MATTMCCA/Heliotrope/Case/OSHCut/036.jpeg

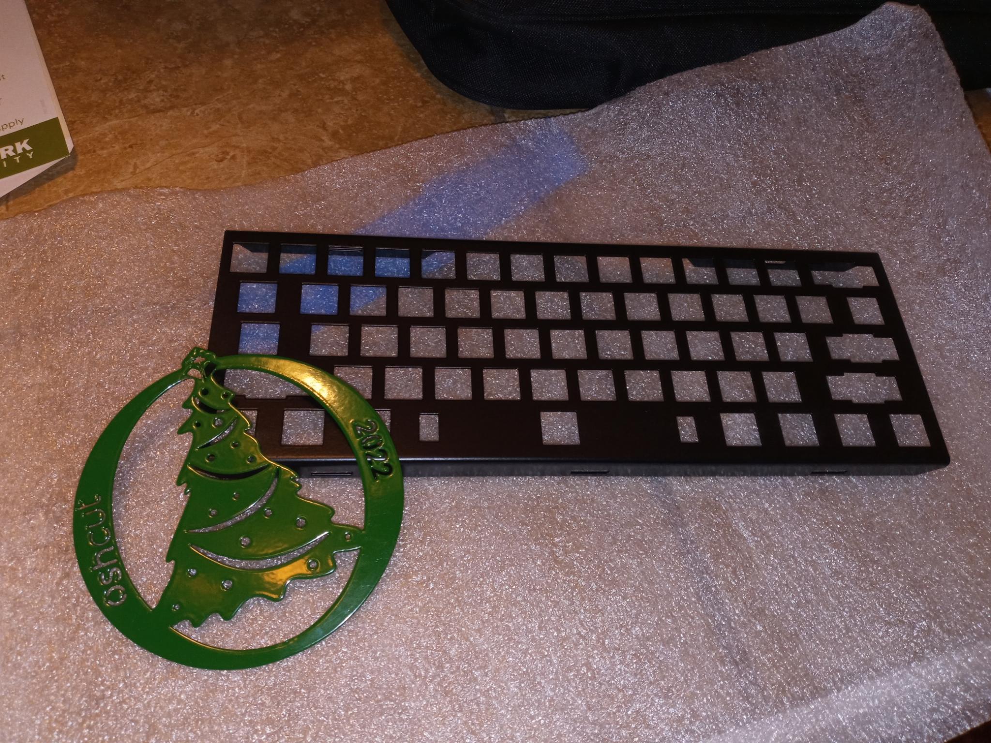
Case/OSHCut/036.jpeg
