MATTMCCA/Heliotrope/Case/ProtoTools/048.jpeg

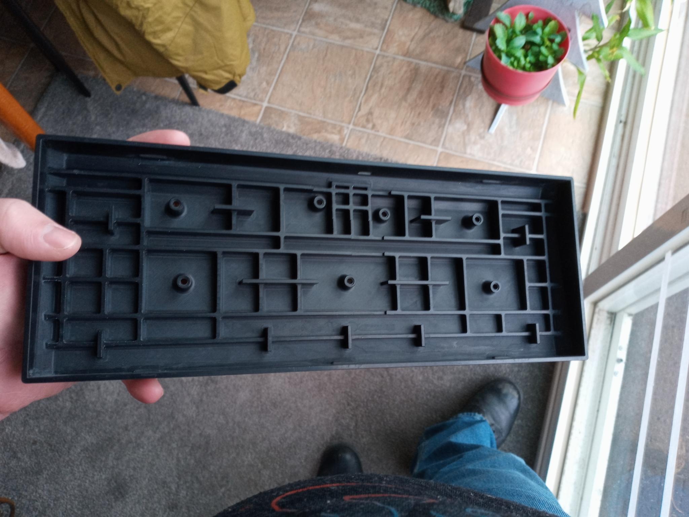
Case/ProtoTools/048.jpeg
